D3V41R/Walky_Talky-/Core/Src/Codec2/codebookjmv.c

/* THIS IS A GENERATED FILE. Edit generate_codebook.c and its input */

/*
 * This intermediary file and the files that used to create it are under 
 * The LGPL. See the file COPYING.
 */

#include "defines.h"

  /* /home/zahir/codec2/src/codebook/lspjmv1.txt */
#ifdef __EMBEDDED__
static const float codes0[] = {
#else
static float codes0[] = {
#endif
  0.435217,  0.668864,  1.0103,  1.22042,  1.50398,  1.78468,  2.13546,  2.35747,  2.61891,  2.73804,
  0.179285,  0.33316,  0.500638,  0.79695,  1.03999,  1.23497,  1.6523,  1.84823,  2.62556,  2.80497,
  0.268785,  0.356576,  0.595753,  1.04434,  1.24938,  1.42868,  1.68699,  1.86469,  2.33991,  2.5138,
  0.12007,  0.165585,  0.484694,  0.95916,  1.23753,  1.52915,  1.83751,  2.10773,  2.48749,  2.76685,
  0.150214,  0.229487,  0.62824,  0.961255,  1.33706,  1.59831,  1.91974,  2.21786,  2.53732,  2.75956,
  0.268624,  0.34598,  0.569637,  0.754737,  0.916538,  1.50854,  1.78635,  1.95442,  2.36953,  2.50182,
  0.246064,  0.468874,  0.662711,  0.890015,  1.14715,  1.51043,  1.78106,  2.09594,  2.65539,  2.80037,
  0.191631,  0.280628,  0.393229,  0.611761,  1.42017,  1.70774,  1.87303,  2.10155,  2.28035,  2.49949,
  0.361668,  0.507047,  0.789974,  1.04599,  1.50238,  1.67703,  1.90534,  2.16255,  2.43226,  2.59087,
  0.20816,  0.294285,  0.448634,  0.694229,  0.872517,  1.07032,  1.70335,  2.16874,  2.42619,  2.60366,
  0.316939,  0.513618,  0.705487,  0.917036,  1.17599,  1.31114,  1.6186,  2.03784,  2.45052,  2.5794,
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
  -0.063079,  -0.130699,  0.0705,  0.033468,  -0.019802,
  -0.061011,  0.094839,  -0.040122,  0.118409,  0.05695,
  0.086391,  -0.006615,  0.045337,  -0.04419,  -0.106474,
  -0.081912,  0.067557,  -0.031649,  -0.014437,  0.057585,
  -0.121755,  -0.049113,  0.057109,  -0.049872,  0.044104,
  0.064705,  -0.091589,  0.037286,  -0.048606,  -0.045398,
  0.003456,  0.05723,  0.006262,  -0.055206,  -0.063871,
  -0.005249,  0.081783,  0.134969,  -0.002331,  0.052643,
  -0.093346,  0.072093,  0.116025,  -0.031453,  -0.006012,
  -0.038574,  -0.030841,  0.010288,  0.02442,  0.051657,
  -0.086584,  0.046381,  0.00541,  0.052622,  -0.072741,
  0.079023,  0.078099,  -0.093912,  0.005477,  -0.006721,
  0.100232,  -0.017587,  0.044819,  0.036655,  0.02158,
  -0.006829,  -0.050076,  -0.00302,  0.088246,  0.01356,
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
};

const struct lsp_codebook lsp_cbjmv[] = {
  /* /home/zahir/codec2/src/codebook/lspjmv1.txt */
  {
    10,
    9,
    512,
    codes0
  },
  /* /home/zahir/codec2/src/codebook/lspjmv2.txt */
  {
    5,
    9,
    512,
    codes1
  },
  /* /home/zahir/codec2/src/codebook/lspjmv3.txt */
  {
    5,
    9,
    512,
    codes2
  },
  { 0, 0, 0, 0 }
};
