D3V41R/Walky_Talky-/Core/Src/Codec2/codebooknewamp1.c

/* THIS IS A GENERATED FILE. Edit generate_codebook.c and its input */

/*
 * This intermediary file and the files that used to create it are under 
 * The LGPL. See the file COPYING.
 */

#include "defines.h"

  /* /home/zahir/codec2/src/codebook/train_120_1.txt */
#ifdef __EMBEDDED__
static const float codes0[] = {
#else
static float codes0[] = {
#endif
  6.7484,  7.6125,  6.0332,  5.2789,  1.5239,  2.2353,  2.0748,  0.5289,  0.8748,  2.5432,  -2.2863,  -3.191,  -0.0434,  -1.9857,  -3.3605,  0.7069,  -5.9493,  -0.5672,  -0.6798,  -18.0977,
  4.0503,  3.9086,  2.9225,  2.3773,  0.658,  -0.4363,  -0.0644,  2.4063,  1.3428,  2.4542,  0.5275,  0.982,  -1.3277,  0.6811,  0.0273,  -0.1838,  -0.0222,  -0.6478,  -2.2405,  -17.4152,
  13.3284,  12.1212,  10.6531,  9.8214,  11.0388,  15.812,  19.711,  16.5488,  16.1068,  15.8771,  7.2553,  4.2486,  -6.0036,  -12.5476,  -20.1299,  -28.2803,  -25.3971,  -21.7907,  -11.5143,  -26.859,
  21.4405,  18.4703,  17.8693,  14.9679,  11.2994,  6.4906,  4.7717,  0.1959,  -0.8801,  1.8991,  1.9793,  -4.9755,  -7.7852,  -10.0492,  -8.5295,  -8.2893,  -4.1203,  -12.4072,  -16.166,  -26.1817,
  4.0023,  3.8279,  1.2681,  1.0053,  0.7002,  -0.3886,  3.4465,  -1.4055,  -6.7846,  -2.3345,  -2.905,  -0.1344,  3.4192,  2.4319,  10.0096,  3.9279,  0.6807,  0.322,  -3.8325,  -17.2565,
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
};

const struct lsp_codebook newamp1vq_cb[] = {
  /* /home/zahir/codec2/src/codebook/train_120_1.txt */
  {
    20,
    9,
    512,
    codes0
  },
  /* /home/zahir/codec2/src/codebook/train_120_2.txt */
  {
    20,
    9,
    512,
    codes1
  },
  { 0, 0, 0, 0 }
};
