D3V41R/Walky_Talky-/Core/Src/Codec2/codebooknewamp2.c

/* THIS IS A GENERATED FILE. Edit generate_codebook.c and its input */

/*
 * This intermediary file and the files that used to create it are under 
 * The LGPL. See the file COPYING.
 */

#include "defines.h"

  /* /home/zahir/codec2/src/codebook/codes_450.txt */
#ifdef __EMBEDDED__
static const float codes0[] = {
#else
static float codes0[] = {
#endif
  11.9178,  14.1558,  15.0079,  16.3077,  17.3822,  18.2611,  17.4655,  14.7258,  9.9322,  5.5523,  2.3108,  -0.5449,  -3.1948,  -5.2578,  -6.672,  -7.0718,  -6.2242,  -3.5271,  -0.4724,  -0.6426,  -5.5883,  -11.069,  -13.9474,  -14.1999,  -11.6213,  -9.2487,  -10.7685,  -15.1688,  -17.7995,  4.747,  5.3362,  4.5288,  2.041,  -0.2507,  -1.4078,  -1.9789,  -2.0773,  -2.8836,  -2.6876,  -5.367,  -21.5899,
  20.9429,  19.2708,  15.6619,  12.7137,  9.1871,  6.4196,  3.1467,  1.6784,  0.8989,  1.2827,  1.4966,  0.1254,  -2.5426,  -4.515,  -6.1876,  -6.3874,  -6.0478,  -5.9793,  -6.4367,  -5.2532,  -2.2523,  -0.5109,  1.6273,  0.3551,  -4.439,  -9.5465,  -11.7875,  -11.3329,  -11.5883,  4.4211,  3.0334,  0.1707,  -1.8877,  -1.6176,  -0.7003,  0.0063,  0.8933,  -0.3305,  -0.5297,  -3.459,  -17.2335,
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
};

const struct lsp_codebook newamp2vq_cb[] = {
  /* /home/zahir/codec2/src/codebook/codes_450.txt */
  {
    41,
    9,
    500,
    codes0
  },
  { 0, 0, 0, 0 }
};
