D3V41R/Walky_Talky-/Core/Src/Codec2/codebookge.c

/* THIS IS A GENERATED FILE. Edit generate_codebook.c and its input */

/*
 * This intermediary file and the files that used to create it are under 
 * The LGPL. See the file COPYING.
 */

#include "defines.h"

  /* /home/zahir/codec2/src/codebook/gecb.txt */
#ifdef __EMBEDDED__
static const float codes0[] = {
#else
static float codes0[] = {
#endif
  2.71,  12.0184,
  0.04675,  -2.73881,
  0.120993,  8.38895,
  -1.58028,  -0.892307,
  1.19307,  -1.91561,
  0.187101,  -3.27679,
  0.332251,  -7.66455,
  -1.47944,  31.2461,
  1.52761,  27.7095,
  -0.524379,  5.25012,
  0.55333,  7.4388,
  -0.843451,  -1.95299,
  2.26389,  8.61029,
  0.143143,  2.36549,
  0.616506,  1.28427,
  -1.71133,  22.0967,
  1.00813,  17.3965,
  -0.106718,  1.41891,
  -0.136246,  14.2736,
  -1.70909,  -20.5319,
  1.65787,  -3.39107,
  0.138049,  -4.95785,
  0.536729,  -1.94375,
  0.196307,  36.8519,
  1.27248,  22.5565,
  -0.670219,  -1.90604,
  0.382092,  6.40113,
  -0.756911,  -4.90102,
  1.82931,  4.6138,
  0.318794,  0.73683,
  0.612815,  -2.07505,
  -0.410151,  24.7871,
  1.77602,  13.1909,
  0.106457,  -0.104492,
  0.192206,  10.1838,
  -1.82442,  -7.71565,
  0.931346,  4.34835,
  0.308813,  -4.086,
  0.397143,  -11.8089,
  -0.048715,  41.2273,
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
};

const struct lsp_codebook ge_cb[] = {
  /* /home/zahir/codec2/src/codebook/gecb.txt */
  {
    2,
    8,
    256,
    codes0
  },
  { 0, 0, 0, 0 }
};
