D3V41R/Walky_Talky-/Core/Src/Codec2/codebookd.c

/* THIS IS A GENERATED FILE. Edit generate_codebook.c and its input */

/*
 * This intermediary file and the files that used to create it are under 
 * The LGPL. See the file COPYING.
 */

#include "defines.h"

  /* /home/zahir/codec2/src/codebook/dlsp1.txt */
#ifdef __EMBEDDED__
static const float codes0[] = {
#else
static float codes0[] = {
#endif
  25,
  50,
  75,
  100,
  125,
  150,
  175,
  200,
  225,
  250,
  275,
  300,
  325,
  350,
  375,
  400,
  425,
  450,
  475,
  500,
  525,
  550,
  575,
  600,
  625,
  650,
  675,
  700,
  725,
  750,
  775,
  800
};
  /* /home/zahir/codec2/src/codebook/dlsp2.txt */
#ifdef __EMBEDDED__
static const float codes1[] = {
#else
static float codes1[] = {
#endif
  25,
  50,
  75,
  100,
  125,
  150,
  175,
  200,
  225,
  250,
  275,
  300,
  325,
  350,
  375,
  400,
  425,
  450,
  475,
  500,
  525,
  550,
  575,
  600,
  625,
  650,
  675,
  700,
  725,
  750,
  775,
  800
};
  /* /home/zahir/codec2/src/codebook/dlsp3.txt */
#ifdef __EMBEDDED__
static const float codes2[] = {
#else
static float codes2[] = {
#endif
  25,
  50,
  75,
  100,
  125,
  150,
  175,
  200,
  225,
  250,
  275,
  300,
  325,
  350,
  375,
  400,
  425,
  450,
  475,
  500,
  525,
  550,
  575,
  600,
  625,
  650,
  675,
  700,
  725,
  750,
  775,
  800
};
  /* /home/zahir/codec2/src/codebook/dlsp4.txt */
#ifdef __EMBEDDED__
static const float codes3[] = {
#else
static float codes3[] = {
#endif
  25,
  50,
  75,
  100,
  125,
  150,
  175,
  200,
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
  /* /home/zahir/codec2/src/codebook/dlsp8.txt */
  {
    1,
    5,
    32,
    codes7
  },
  /* /home/zahir/codec2/src/codebook/dlsp9.txt */
  {
    1,
    5,
    32,
    codes8
  },
  /* /home/zahir/codec2/src/codebook/dlsp10.txt */
  {
    1,
    5,
    32,
    codes9
  },
  { 0, 0, 0, 0 }
};
